tony92151/Lemon_minibot/gazebo/minibot_simulation/meshes/ar/ar_image/local1.png

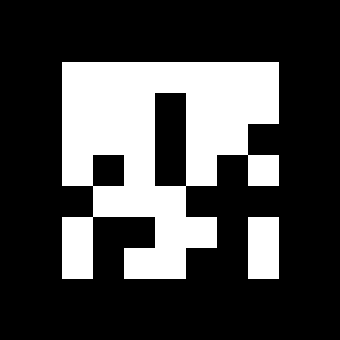
gazebo/minibot_simulation/meshes/ar/ar_image/local1.png
