tony92151/Lemon_minibot/image/ar_image/MarkerData_4567.png

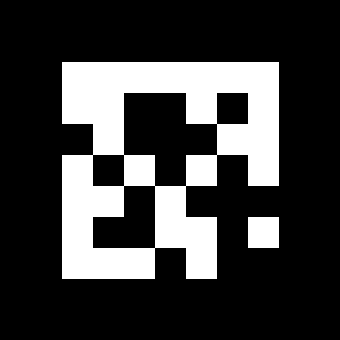
image/ar_image/MarkerData_4567.png
