tony92151/Lemon_minibot/image/ar_image/MarkerData_6789.png

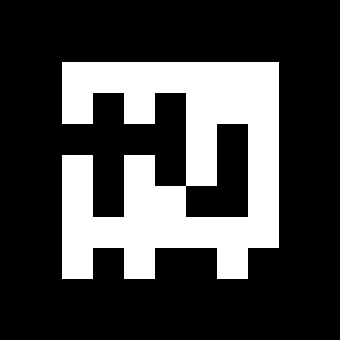
image/ar_image/MarkerData_6789.png
