tony92151/Lemon_minibot/image/gazebo_home.png

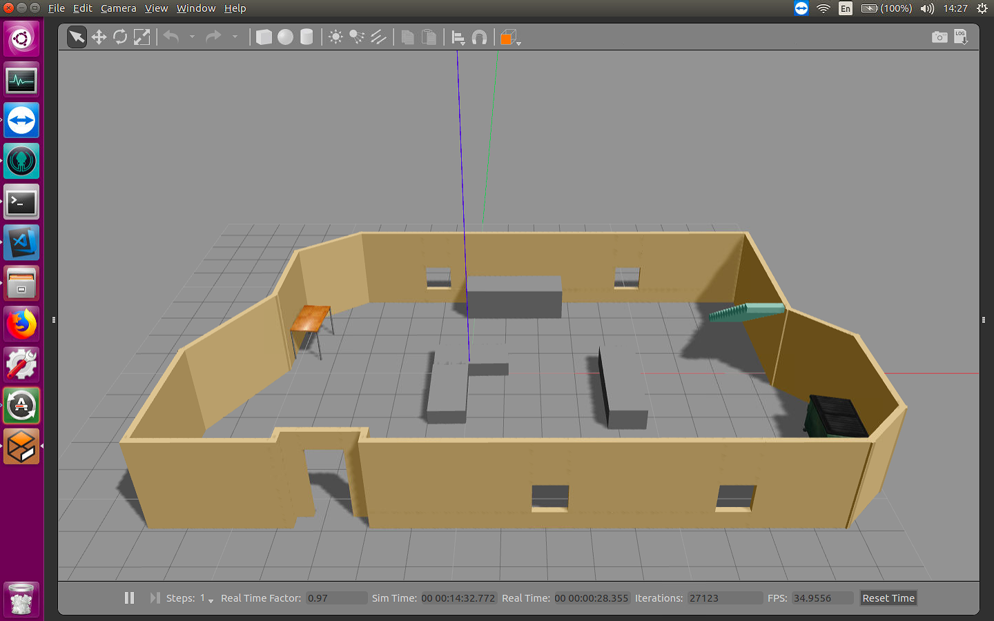
image/gazebo_home.png
