tony92151/Lemon_minibot/image/image2.JPG

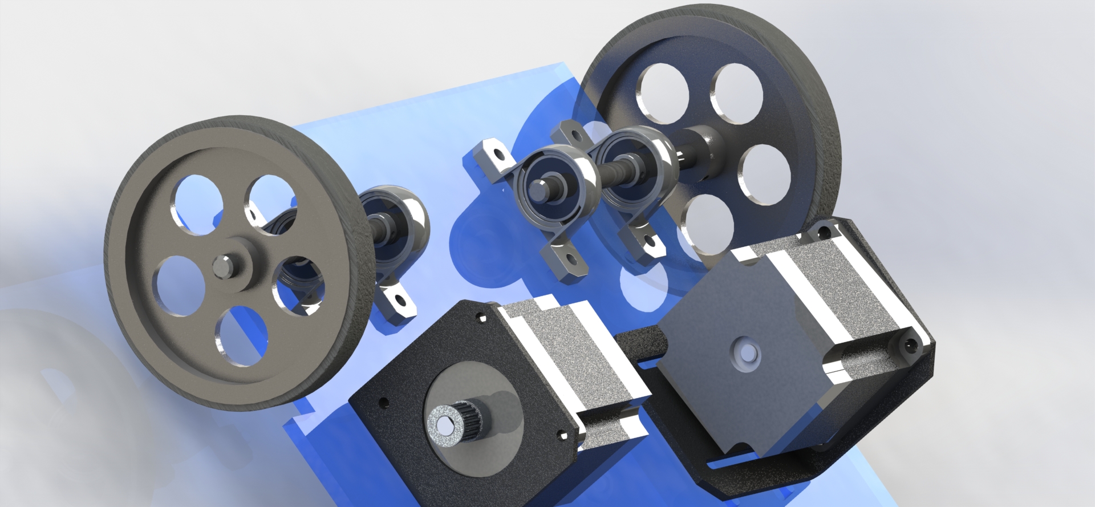
image/image2.JPG
