tony92151/Lemon_minibot/image/image3.JPG

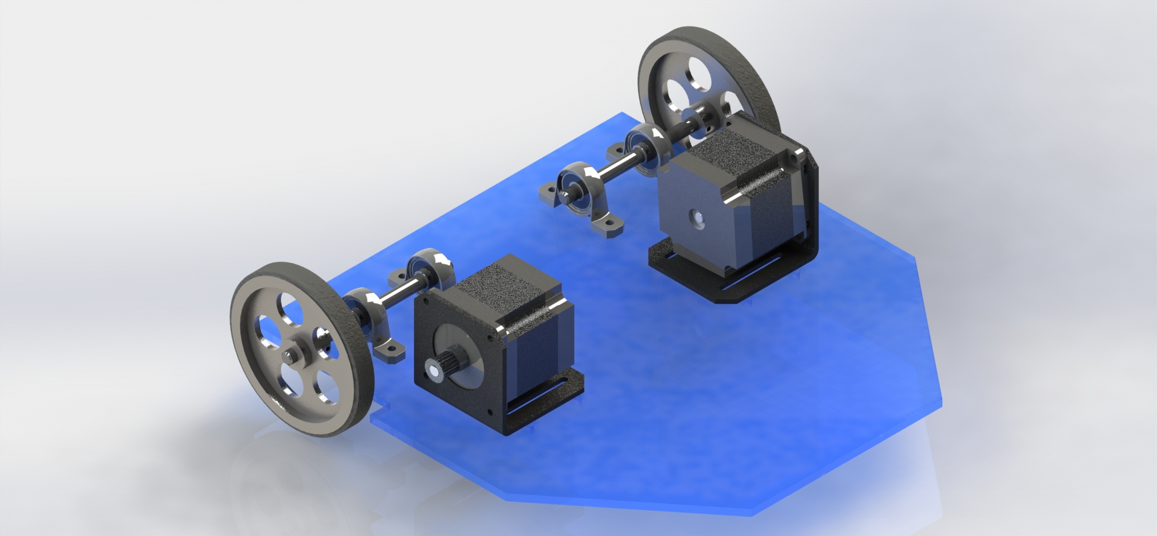
image/image3.JPG
