tony92151/Lemon_minibot/hardware/sw2016/GT2-60T-635B.SLDPRT

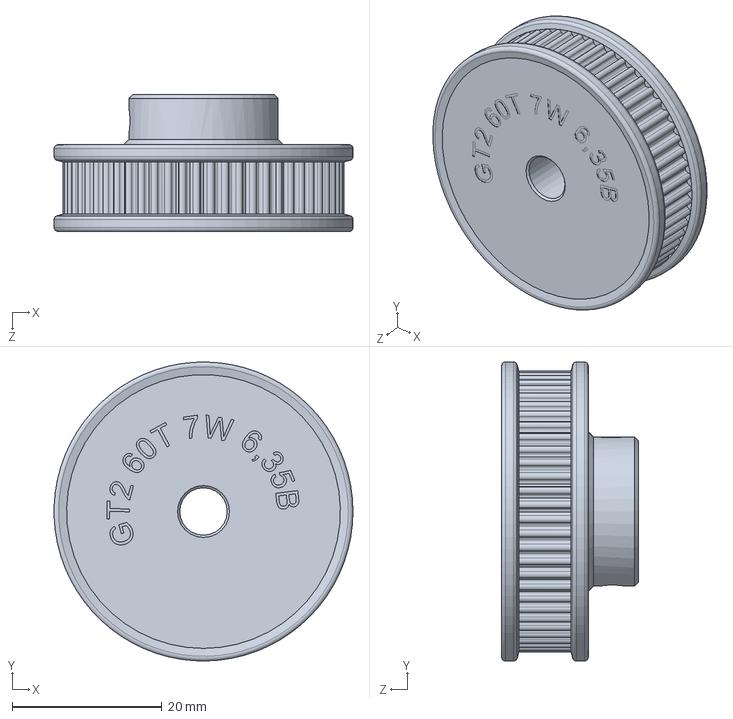
[picture p43: CAD file, 2019-01-13]
hardware/sw2016/GT2-60T-635B.SLDPRT
40.0 x 40.0 x 18.3 mm
