tony92151/Lemon_minibot/gazebo/sw2016/base.SLDPRT

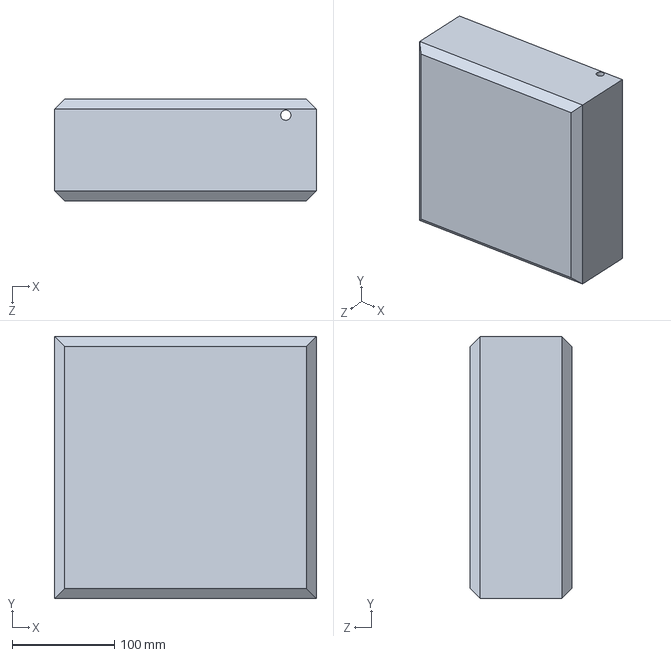
[picture p44: CAD file, 2018-11-05]
gazebo/sw2016/base.SLDPRT
256.0 x 256.0 x 100.0 mm
