tony92151/Lemon_minibot/hardware/solidworks2018/cooper.SLDPRT

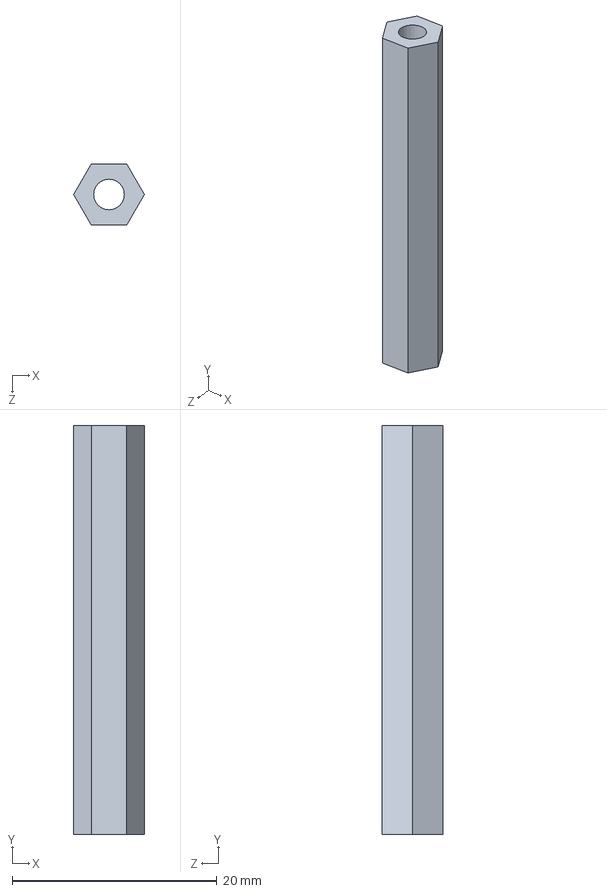
[picture p45: CAD file, 2018-09-20]
hardware/solidworks2018/cooper.SLDPRT
6.93 x 40.0 x 6.00 mm
