tony92151/Lemon_minibot/gazebo/sw2016/laser.SLDPRT

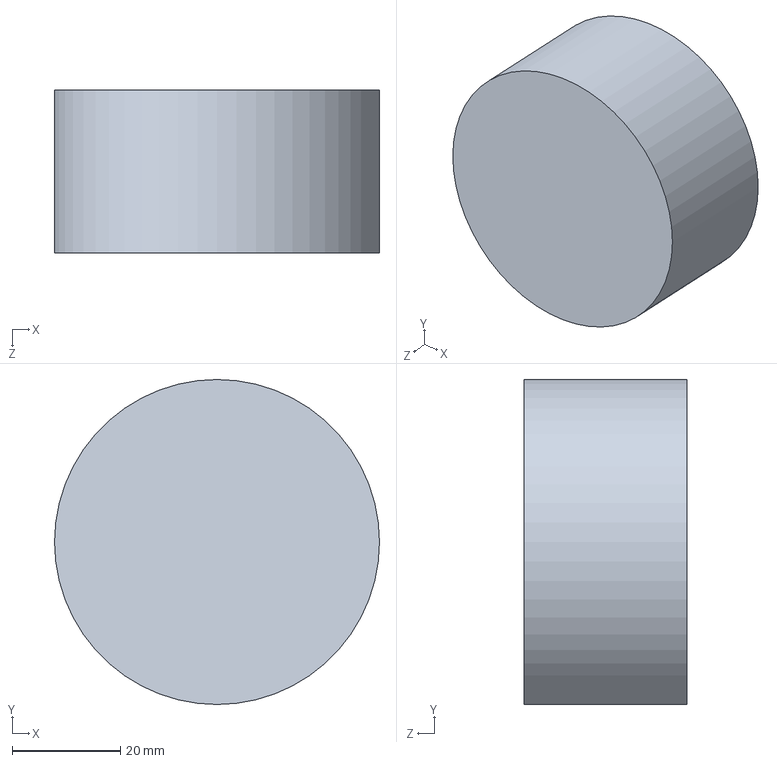
[picture p46: CAD file, 2018-11-05]
gazebo/sw2016/laser.SLDPRT
60.0 x 60.0 x 30.0 mm
