tony92151/Lemon_minibot/hardware/solidworks2018/wheel2.SLDPRT

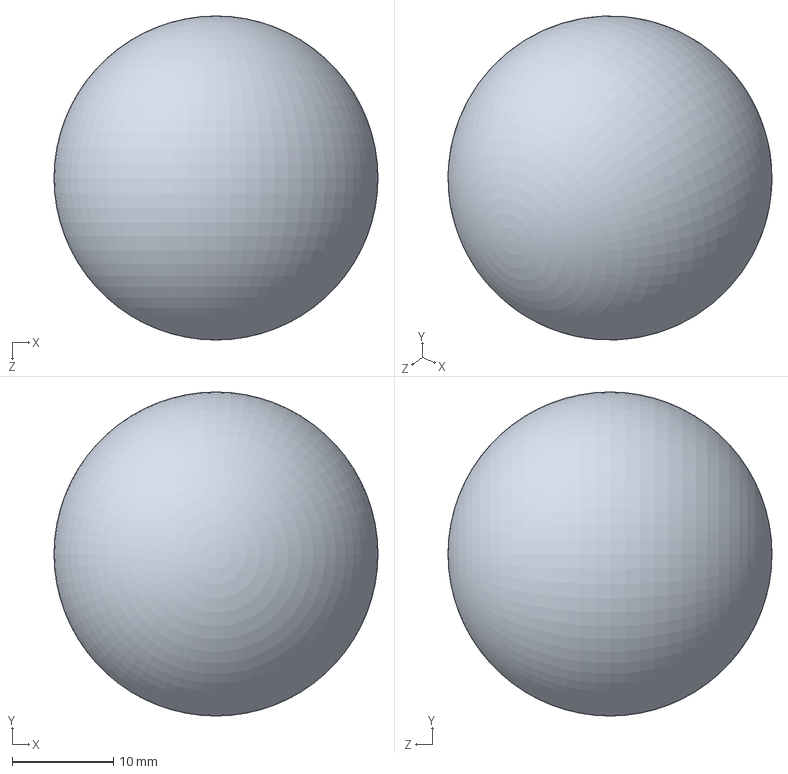
[picture p47: CAD file, 2018-09-20]
hardware/solidworks2018/wheel2.SLDPRT
32.0 x 32.0 x 32.0 mm
