tony92151/Lemon_minibot/hardware/sw2016/MotorMount_NEMA.SLDPRT

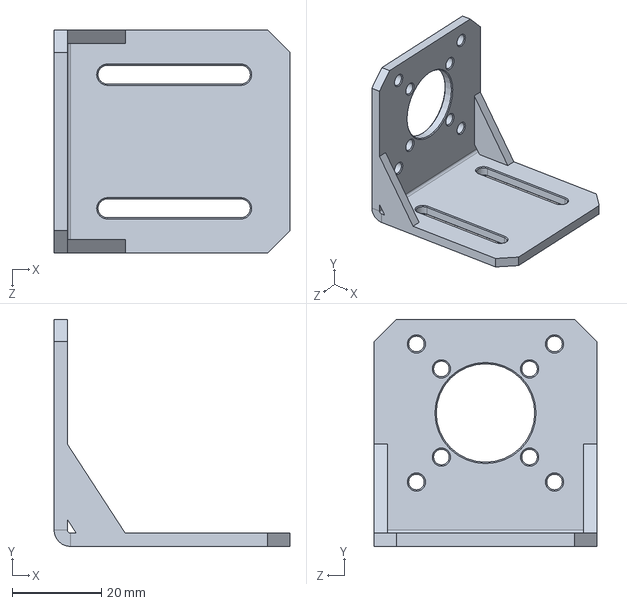
[picture p48: CAD file, 2019-01-13]
hardware/sw2016/MotorMount_NEMA.SLDPRT
53.0 x 51.0 x 50.0 mm
