tony92151/Lemon_minibot/gazebo/sw2016/wheel.SLDPRT

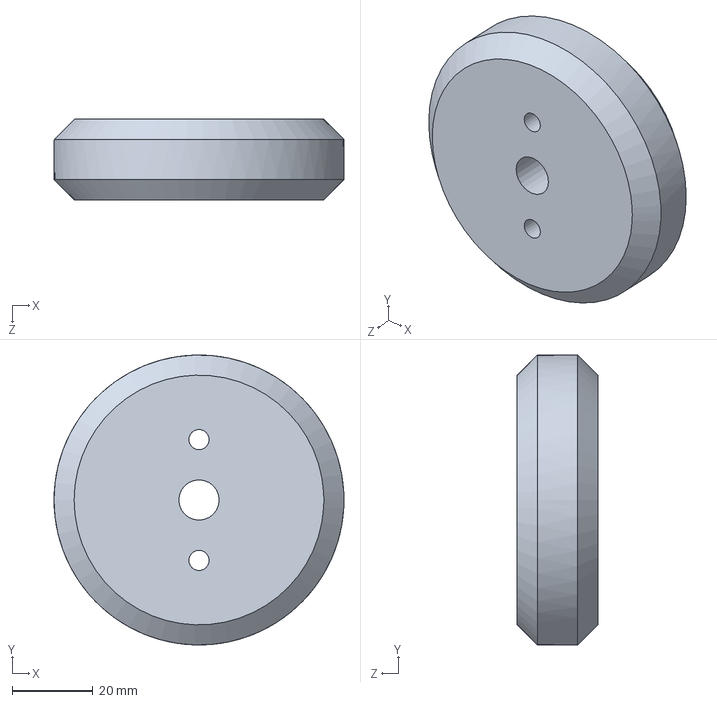
[picture p49: CAD file, 2018-11-05]
gazebo/sw2016/wheel.SLDPRT
72.0 x 72.0 x 20.0 mm
