tony92151/Lemon_minibot/hardware/solidworks2018/waffle_plate - P-BP-A001_3D.sldprt

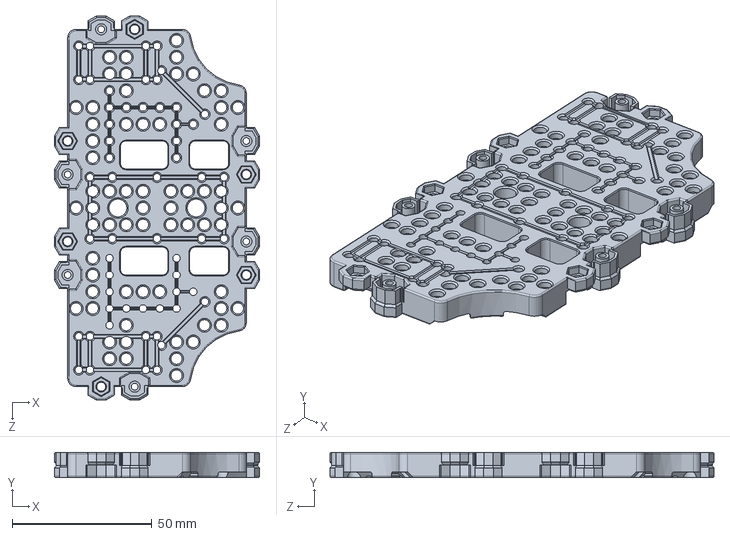
[picture p50: CAD file, 2018-09-20]
hardware/solidworks2018/waffle_plate - P-BP-A001_3D.sldprt
73.5 x 9.00 x 137.5 mm
