tony92151/Lemon_minibot/hardware/sw2016/gt2_20th.SLDPRT

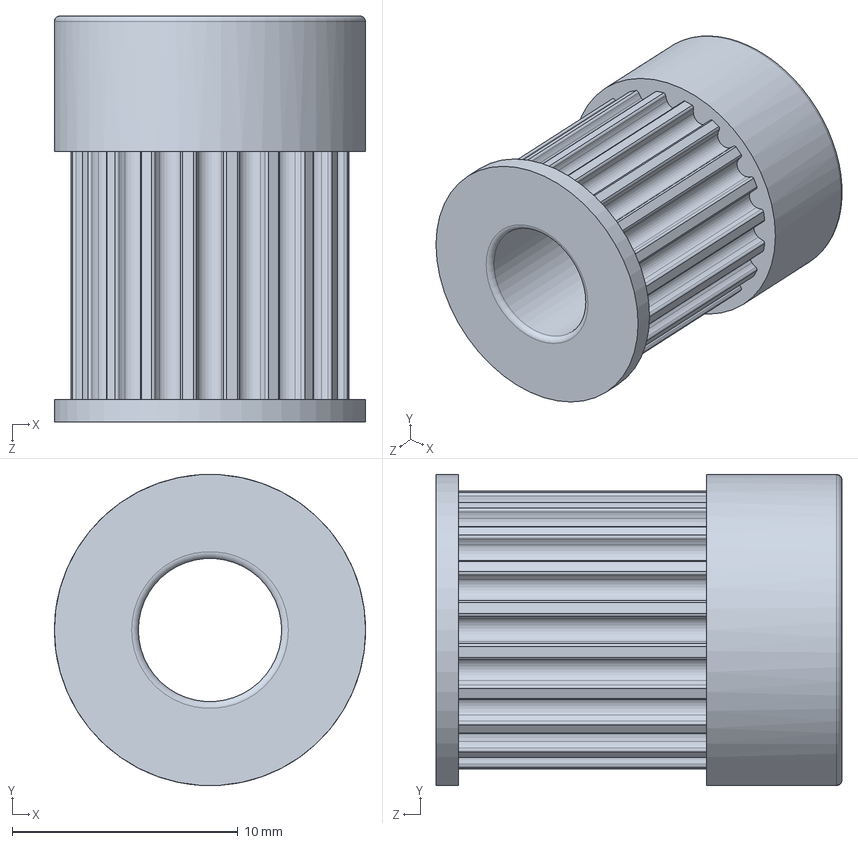
[picture p51: CAD file, 2019-01-13]
hardware/sw2016/gt2_20th.SLDPRT
13.8 x 13.8 x 18.0 mm
