tony92151/Lemon_minibot/hardware/sw2016/wheel_95mm.SLDPRT

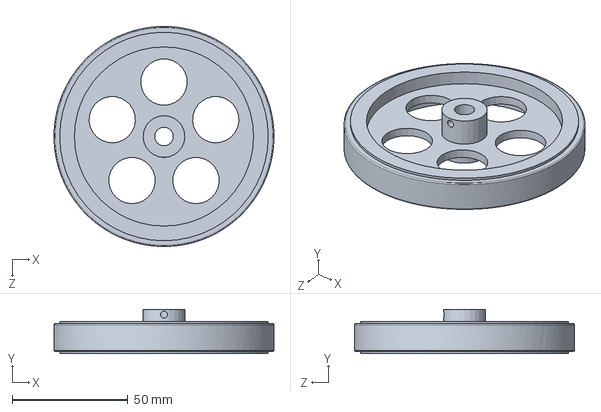
[picture p52: CAD file, 2019-01-13]
hardware/sw2016/wheel_95mm.SLDPRT
95.0 x 19.2 x 95.0 mm
