tony92151/Lemon_minibot/hardware/sw2016/57motor.SLDPRT

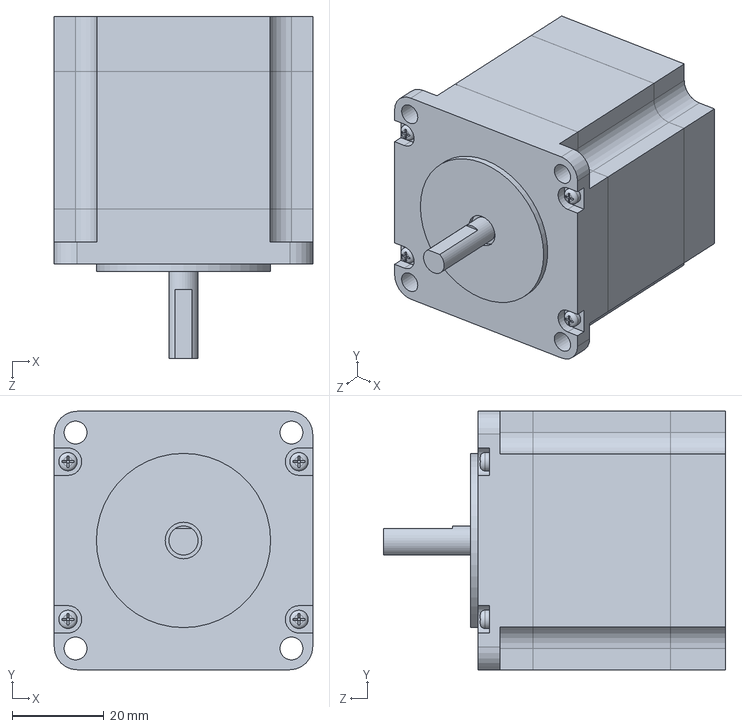
[picture p53: CAD file, 2019-01-13]
hardware/sw2016/57motor.SLDPRT
56.4 x 56.4 x 74.6 mm
