tony92151/Lemon_minibot/hardware/sw2016/base.SLDPRT

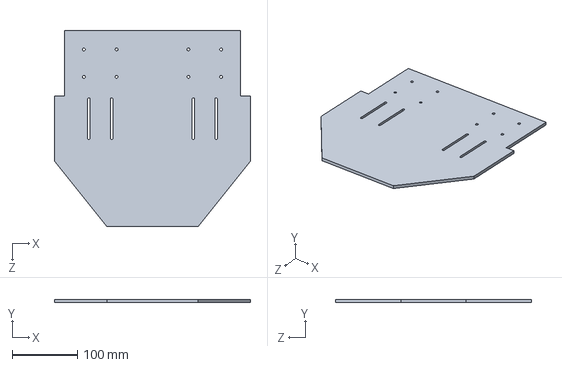
[picture p54: CAD file, 2019-01-13]
hardware/sw2016/base.SLDPRT
300.0 x 5.00 x 300.0 mm
