tony92151/Lemon_minibot/hardware/sw2016/8mm_rod_150mm.SLDPRT

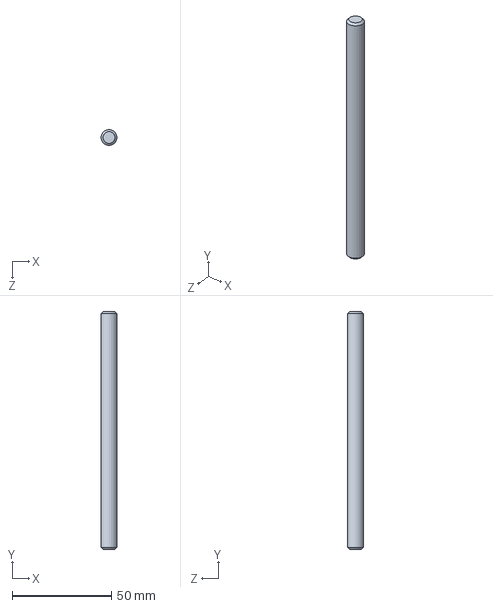
[picture p55: CAD file, 2019-01-13]
hardware/sw2016/8mm_rod_150mm.SLDPRT
8.00 x 120.0 x 8.00 mm
