tony92151/Lemon_minibot/lemon_minibot_control/scripts/camera_flip.py

#!/usr/bin/env python
from __future__ import print_function
 
import sys
import rospy
import cv2
from std_msgs.msg import String
from sensor_msgs.msg import Image
from cv_bridge import CvBridge, CvBridgeError
 
class image_converter:
 
  def __init__(self):
    self.image_pub = rospy.Publisher("/usb_cam/image_raw_flip",Image,queue_size=10)
 
    self.bridge = CvBridge()
    self.image_sub = rospy.Subscriber("/usb_cam/image_raw",Image,self.callback)
 
  def callback(self,data):
    try:
      cv_image = self.bridge.imgmsg_to_cv2(data, "bgr8")
    except CvBridgeError as e:
      print(e)

    cv_image = cv2.flip( cv_image, 0 )
 
    try:
      self.image_pub.publish(self.bridge.cv2_to_imgmsg(cv_image, "bgr8"))
    except CvBridgeError as e:
      print(e)
 
def main(args):
  ic = image_converter()
  rospy.init_node('image_converter', anonymous=True)
  try:
    rospy.spin()
  except KeyboardInterrupt:
    print("Shutting down")
  cv2.destroyAllWindows()
 
if __name__ == '__main__':
    main(sys.argv)
